coldtobi/tobis_cl260_modifications/Axisholder/Axisholder_Screenshot.png

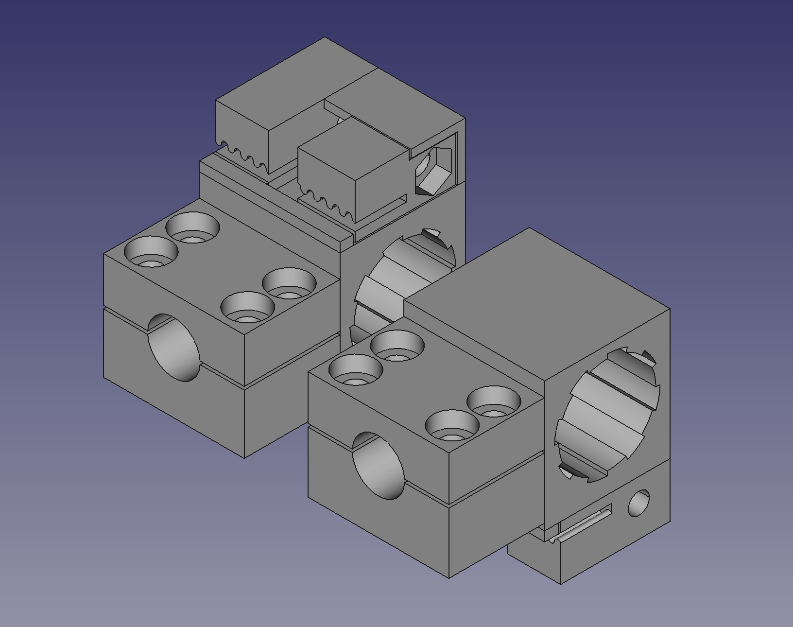
Axisholder/Axisholder_Screenshot.png
