coldtobi/tobis_cl260_modifications/Axisholder/STL/V2/BeltTightener_V2.stl

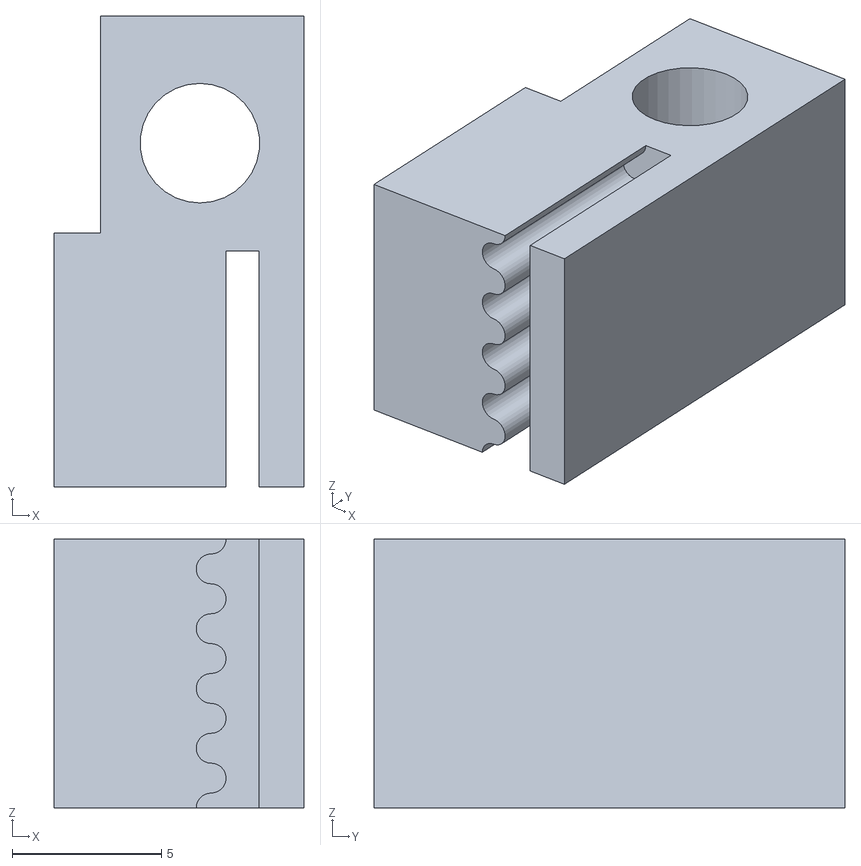
[picture p22: CAD file, 2020-04-19]
Axisholder/STL/V2/BeltTightener_V2.stl
8.35 x 15.8 x 9.00
