coldtobi/tobis_cl260_modifications/Carrier_E3D_Titan/exports/Left-Fan-Nozzle-180°.stl

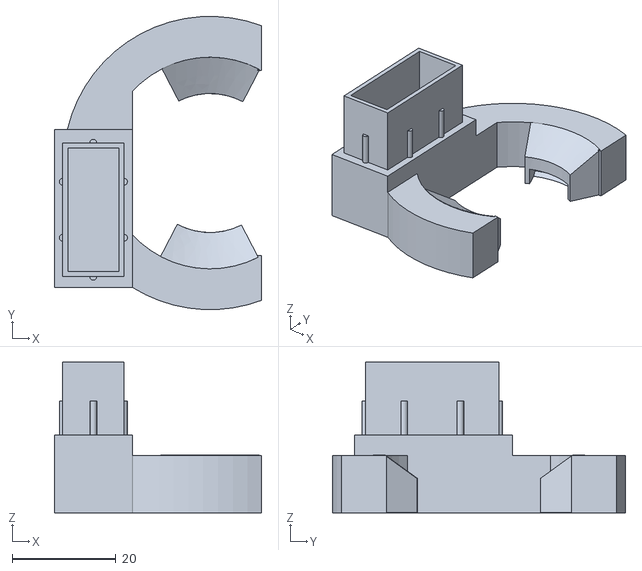
[picture p23: CAD file, 2019-12-24]
Carrier_E3D_Titan/exports/Left-Fan-Nozzle-180°.stl
39.9 x 56.5 x 29.0
