coldtobi/tobis_cl260_modifications/Carrier_E3DV6/STL/Carrier_Part1.stl

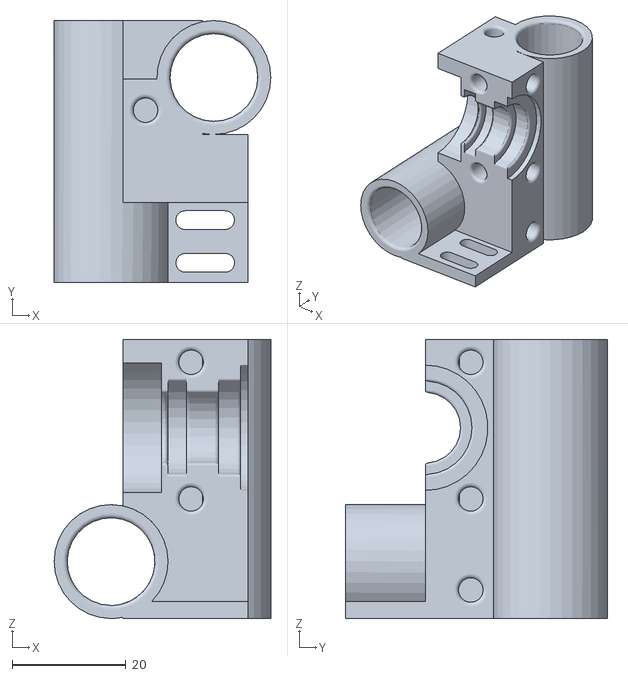
[picture p24: CAD file, 2018-10-11]
Carrier_E3DV6/STL/Carrier_Part1.stl
38.1 x 46.0 x 49.0
