coldtobi/tobis_cl260_modifications/Carrier_E3D_Titan/exports/Left-Fan-Nozzle-Small.stl

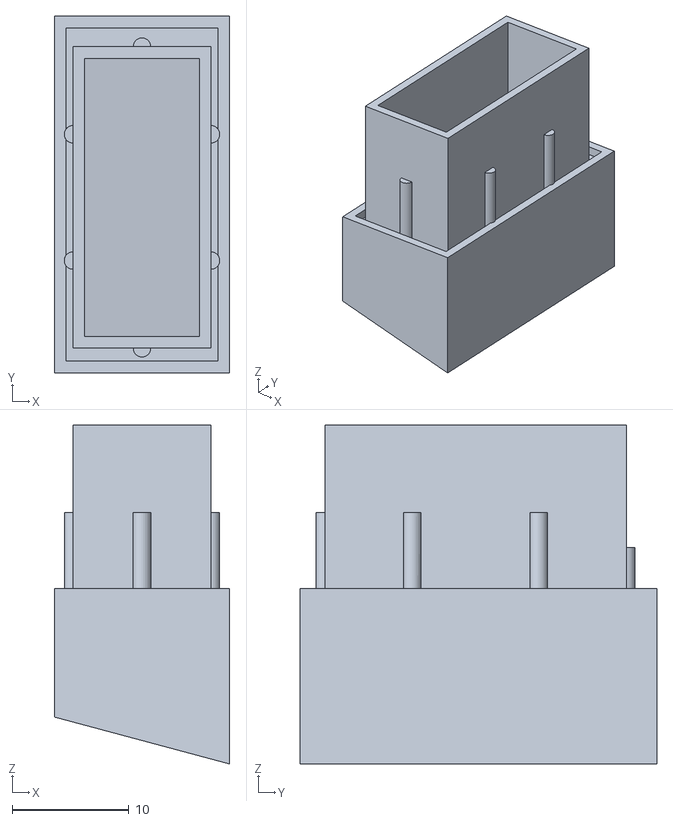
[picture p25: CAD file, 2019-12-24]
Carrier_E3D_Titan/exports/Left-Fan-Nozzle-Small.stl
15.0 x 30.5 x 29.0
