coldtobi/tobis_cl260_modifications/Carrier_E3DV6/STL/FanShroud.stl

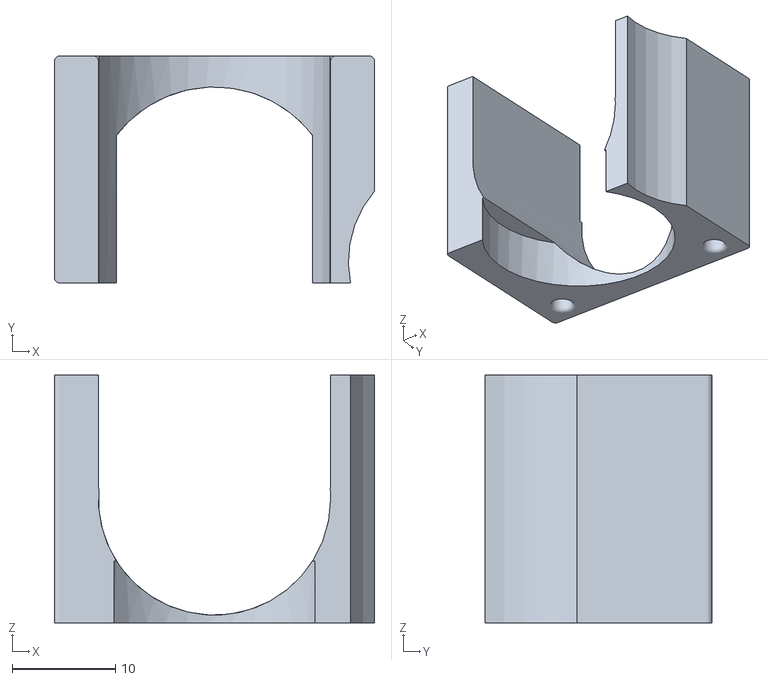
[picture p26: CAD file, 2018-10-11]
Carrier_E3DV6/STL/FanShroud.stl
31.0 x 22.0 x 24.0
