coldtobi/tobis_cl260_modifications/Carrier_E3D_Titan/exports/XY-Carrier.stl

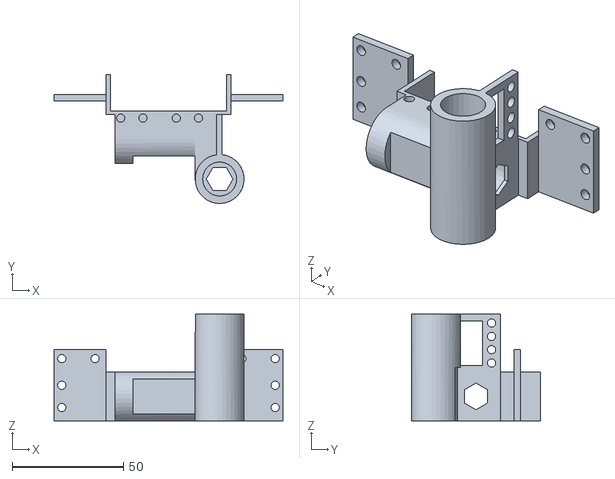
[picture p27: CAD file, 2019-12-24]
Carrier_E3D_Titan/exports/XY-Carrier.stl
103.0 x 58.0 x 48.0
