coldtobi/tobis_cl260_modifications/Z-Axis-Guide/Z-Axis-Guide_Screenshot.png

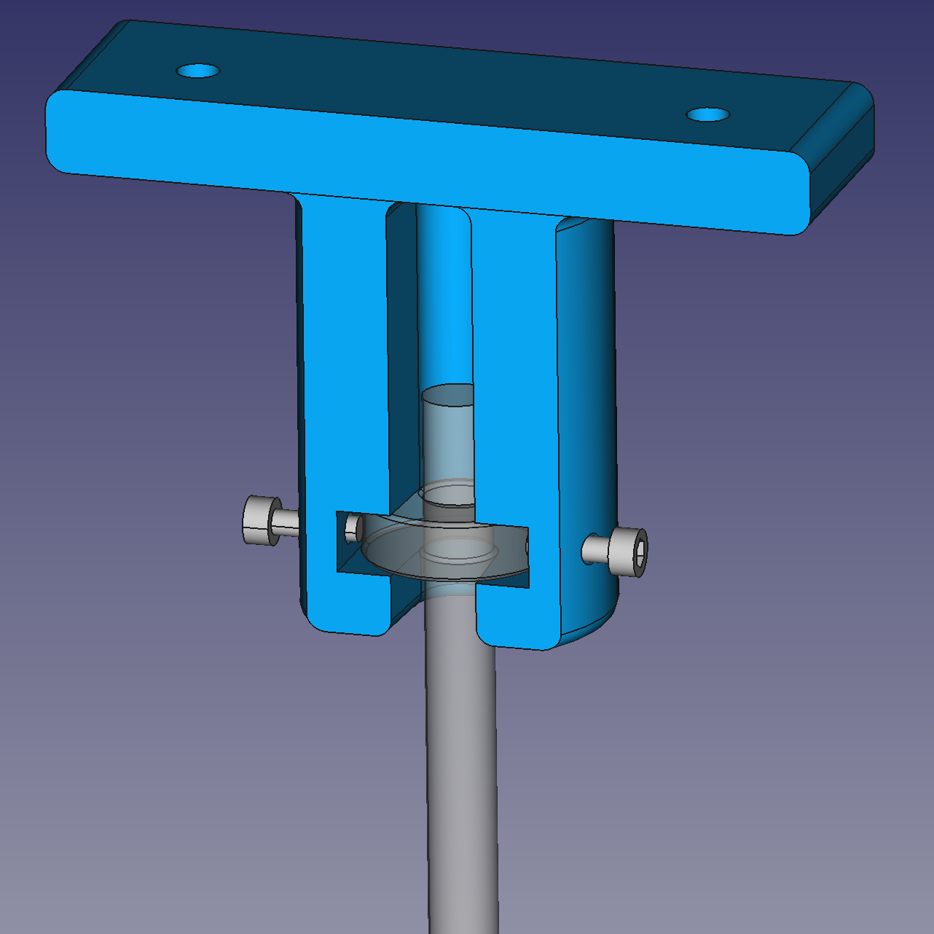
Z-Axis-Guide/Z-Axis-Guide_Screenshot.png
